kbjunky/IIICC/Case/3DP/Keyboard/IIICC-Top_XSwitch.stl

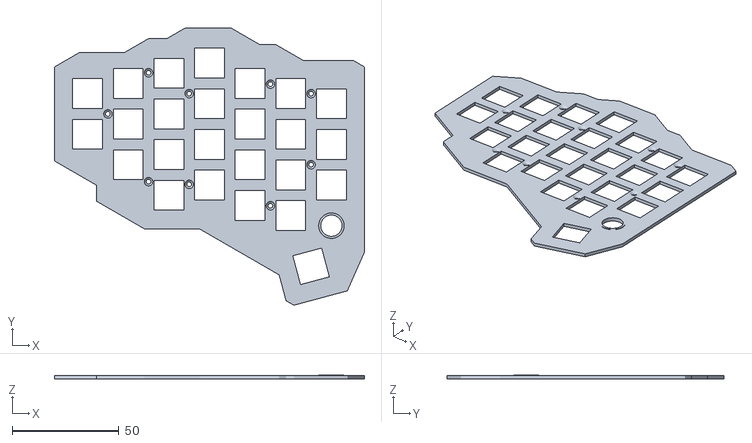
[picture p17: CAD file, 2021-02-26]
Case/3DP/Keyboard/IIICC-Top_XSwitch.stl
145.3 x 130.1 x 1.80
