kbjunky/IIICC/src/IIICC/glcdfont.c

#include "progmem.h"

static const unsigned char PROGMEM font[] = {
    0x00, 0x00, 0x00, 0x00, 0x00, 0x00,
    0x3E, 0x5B, 0x4F, 0x5B, 0x3E, 0x00,
    0x3E, 0x6B, 0x4F, 0x6B, 0x3E, 0x00,
    0x1C, 0x3E, 0x7C, 0x3E, 0x1C, 0x00,
    0x18, 0x3C, 0x7E, 0x3C, 0x18, 0x00,
    0x1C, 0x57, 0x7D, 0x57, 0x1C, 0x00,
    0x1C, 0x5E, 0x7F, 0x5E, 0x1C, 0x00,
    0x00, 0x18, 0x3C, 0x18, 0x00, 0x00,
    0xFF, 0xE7, 0xC3, 0xE7, 0xFF, 0x00,
    0x00, 0x18, 0x24, 0x18, 0x00, 0x00,
    0xFF, 0xE7, 0xDB, 0xE7, 0xFF, 0x00,
    0x30, 0x48, 0x3A, 0x06, 0x0E, 0x00,
    0x26, 0x29, 0x79, 0x29, 0x26, 0x00,
    0x40, 0x7F, 0x05, 0x05, 0x07, 0x00,
    0x40, 0x7F, 0x05, 0x25, 0x3F, 0x00,
    0x5A, 0x3C, 0xE7, 0x3C, 0x5A, 0x00,
    0x7F, 0x3E, 0x1C, 0x1C, 0x08, 0x00,
    0x08, 0x1C, 0x1C, 0x3E, 0x7F, 0x00,
    0x14, 0x22, 0x7F, 0x22, 0x14, 0x00,
    0x5F, 0x5F, 0x00, 0x5F, 0x5F, 0x00,
    0x06, 0x09, 0x7F, 0x01, 0x7F, 0x00,
    0x00, 0x66, 0x89, 0x95, 0x6A, 0x00,
    0x60, 0x60, 0x60, 0x60, 0x60, 0x00,
    0x94, 0xA2, 0xFF, 0xA2, 0x94, 0x00,
    0x08, 0x04, 0x7E, 0x04, 0x08, 0x00,
    0x10, 0x20, 0x7E, 0x20, 0x10, 0x00,
    0x08, 0x08, 0x2A, 0x1C, 0x08, 0x00,
    0x08, 0x1C, 0x2A, 0x08, 0x08, 0x00,
    0x1E, 0x10, 0x10, 0x10, 0x10, 0x00,
    0x0C, 0x1E, 0x0C, 0x1E, 0x0C, 0x00,
    0x30, 0x38, 0x3E, 0x38, 0x30, 0x00,
    0x06, 0x0E, 0x3E, 0x0E, 0x06, 0x00,
    0x00, 0x00, 0x00, 0x00, 0x00, 0x00,
    0x00, 0x00, 0x5F, 0x00, 0x00, 0x00,
    0x00, 0x07, 0x00, 0x07, 0x00, 0x00,
    0x14, 0x7F, 0x14, 0x7F, 0x14, 0x00,
    0x24, 0x2A, 0x7F, 0x2A, 0x12, 0x00,
    0x23, 0x13, 0x08, 0x64, 0x62, 0x00,
    0x36, 0x49, 0x56, 0x20, 0x50, 0x00,
    0x00, 0x08, 0x07, 0x03, 0x00, 0x00,
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
};
